DK9BT/esp32-e22-lora-board/datasheet/Einpressbuchse_M2x4x3,5.jpg

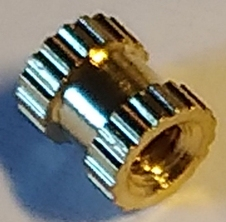
datasheet/Einpressbuchse_M2x4x3,5.jpg
