DK9BT/esp32-e22-lora-board/datasheet/USB-C_vert.PNG

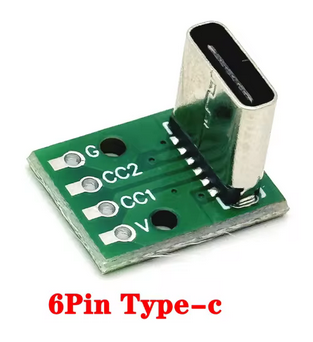
datasheet/USB-C_vert.PNG
