DK9BT/esp32-e22-lora-board/ESP32-E22_V2.1.2/pdf/Bestückungsplan_Front.PNG

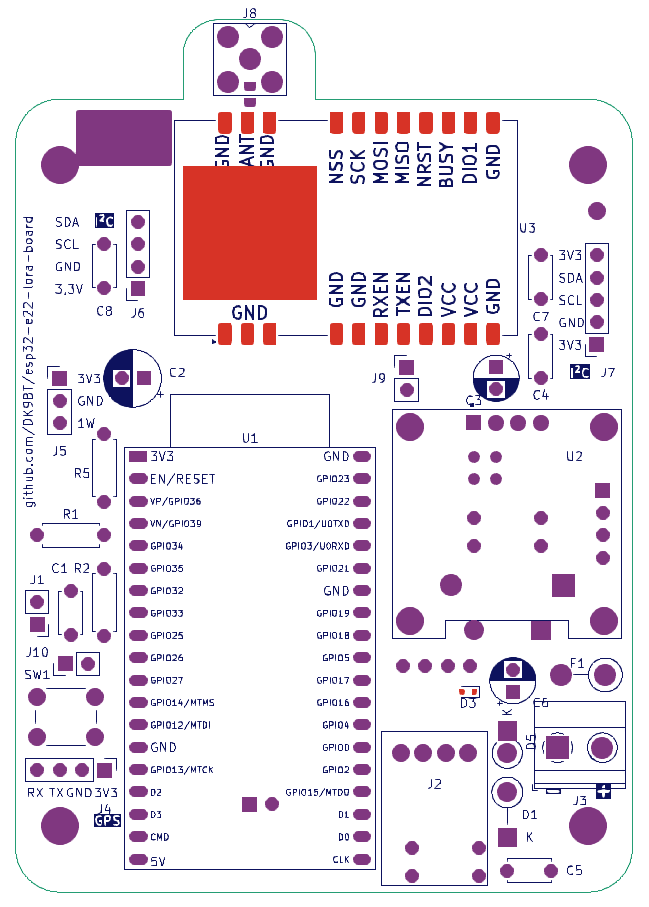
ESP32-E22_V2.1.2/pdf/Bestückungsplan_Front.PNG
