DK9BT/esp32-e22-lora-board/ESP32-E22_V2.1.2/picass/2-5_J3-F1.jpg

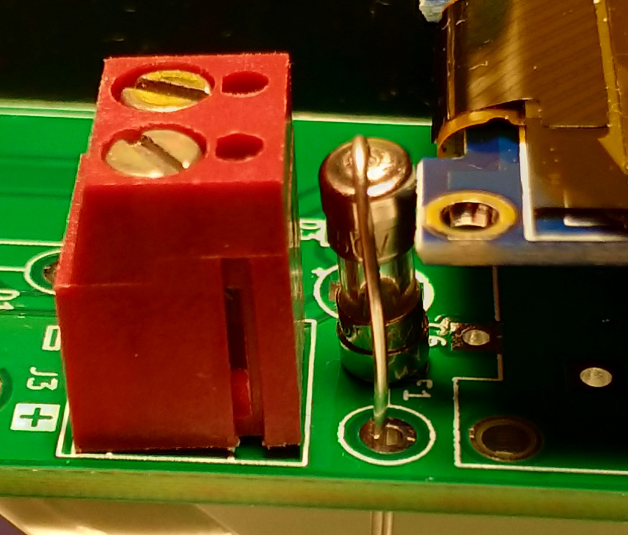
ESP32-E22_V2.1.2/picass/2-5_J3-F1.jpg
