DK9BT/esp32-e22-lora-board/ESP32-E22_V2.1.2/picass/U2+C3+C4.jpg

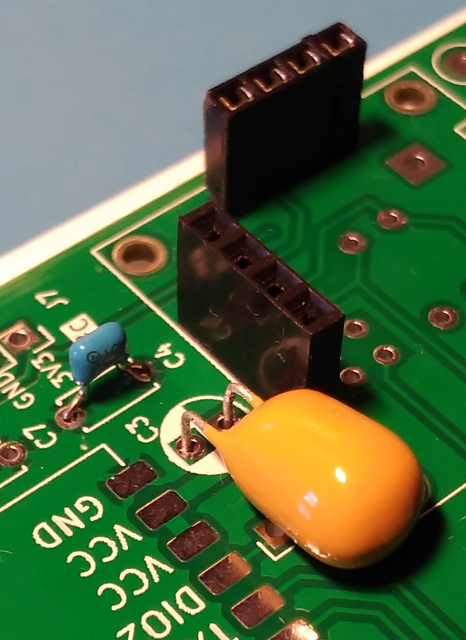
ESP32-E22_V2.1.2/picass/U2+C3+C4.jpg
